OliverHi/RGBW-Controller/Pictures/RGBWController001.jpg

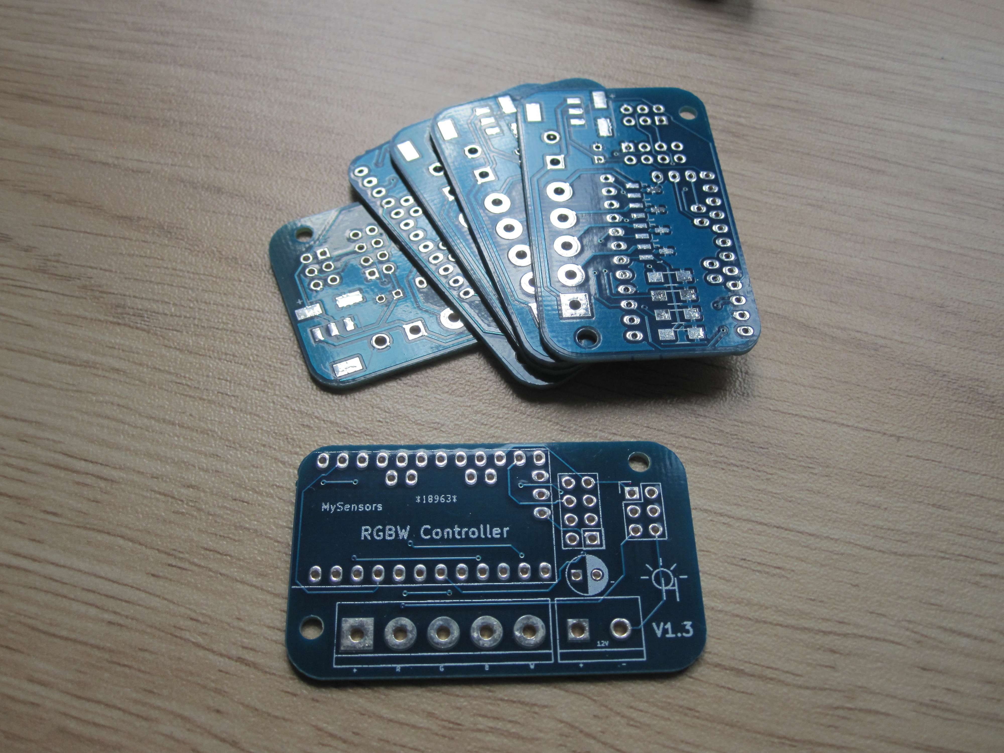
Pictures/RGBWController001.jpg
