OliverHi/RGBW-Controller/Pictures/RGBWController002.jpg

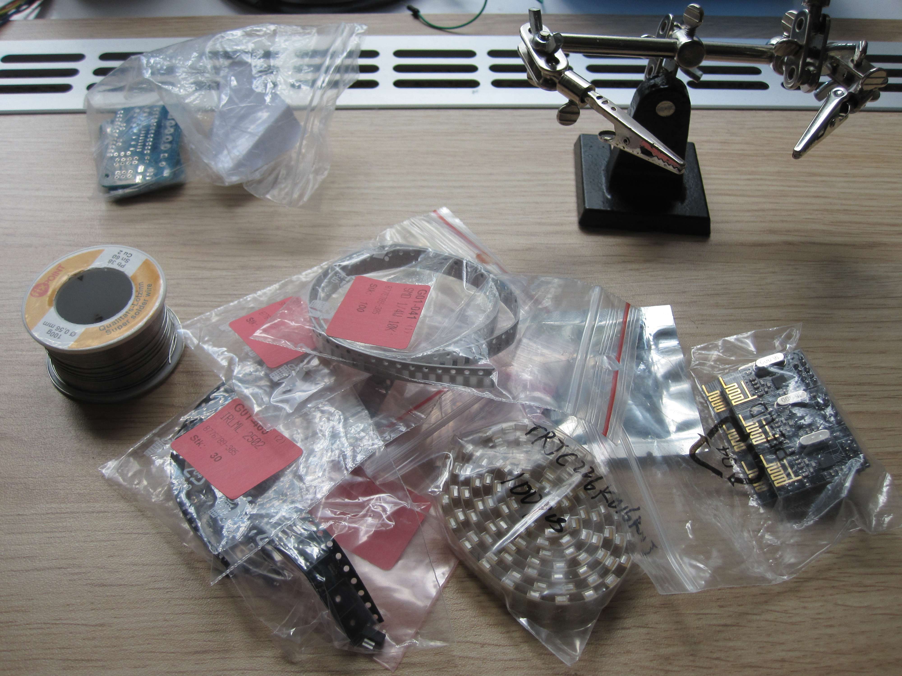
Pictures/RGBWController002.jpg
