OliverHi/RGBW-Controller/Pictures/RGBWController003.jpg

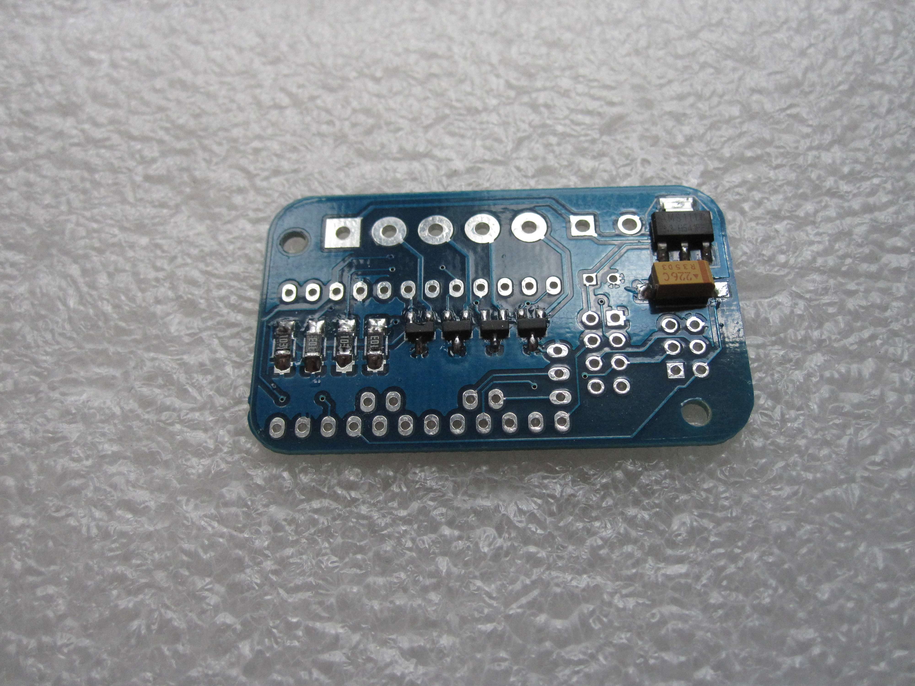
Pictures/RGBWController003.jpg
