OliverHi/RGBW-Controller/Pictures/RGBWController005.jpg

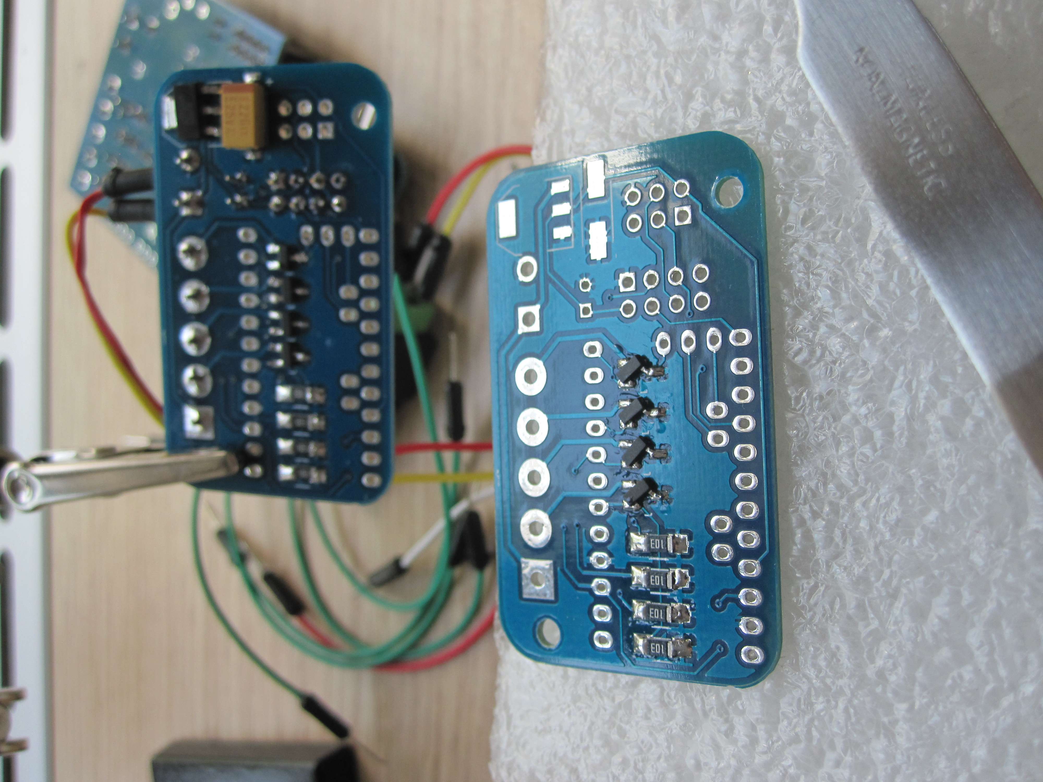
Pictures/RGBWController005.jpg
