OliverHi/RGBW-Controller/Pictures/RGBWController006.jpg

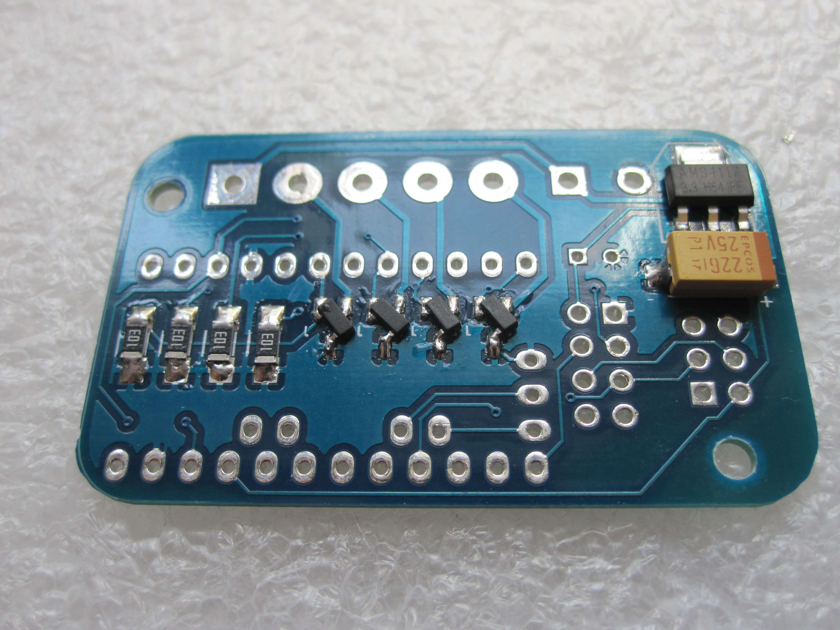
Pictures/RGBWController006.jpg
