OliverHi/RGBW-Controller/Pictures/RGBWController007.jpg

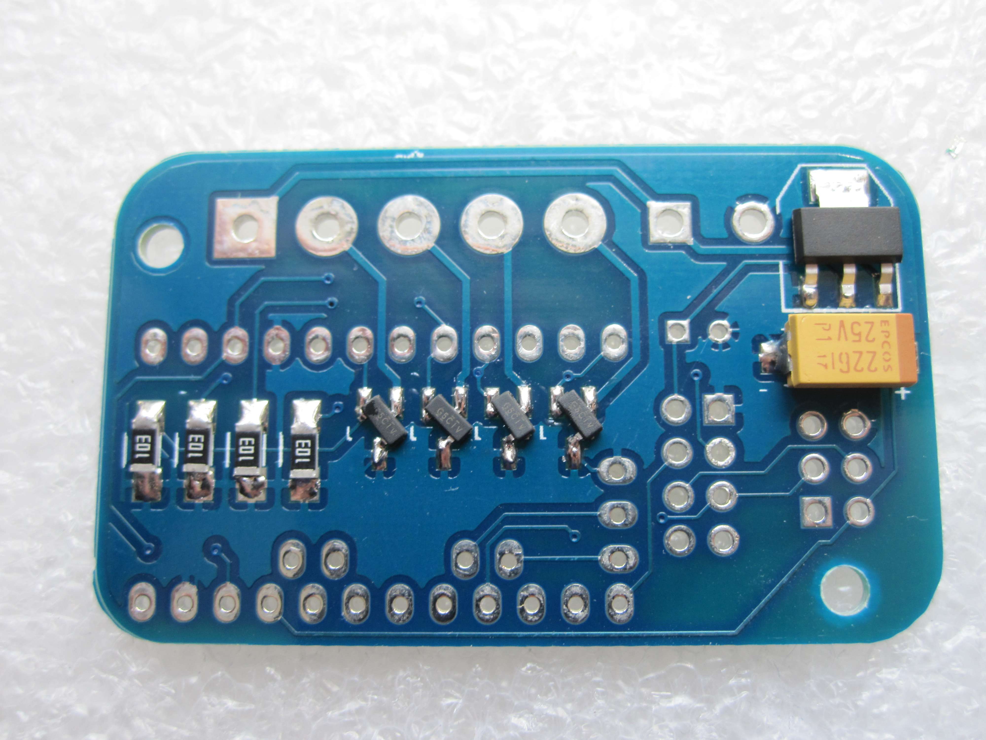
Pictures/RGBWController007.jpg
