OliverHi/RGBW-Controller/Pictures/RGBWController008.jpg

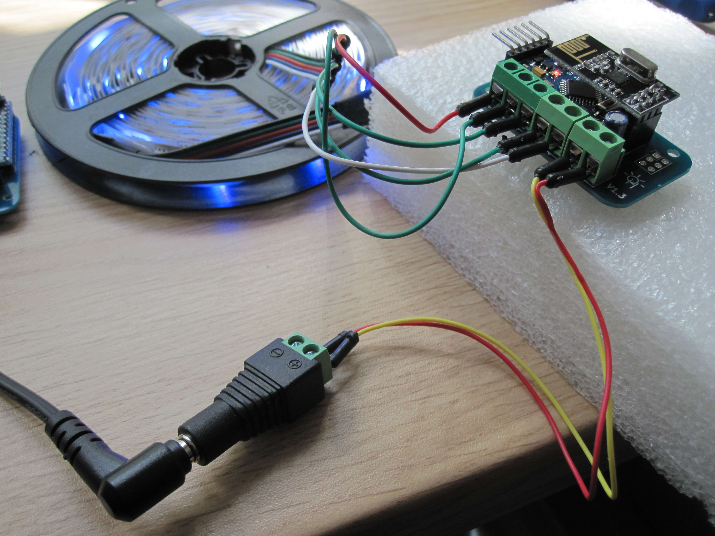
Pictures/RGBWController008.jpg
