OliverHi/RGBW-Controller/Pictures/RGBWController009.jpg

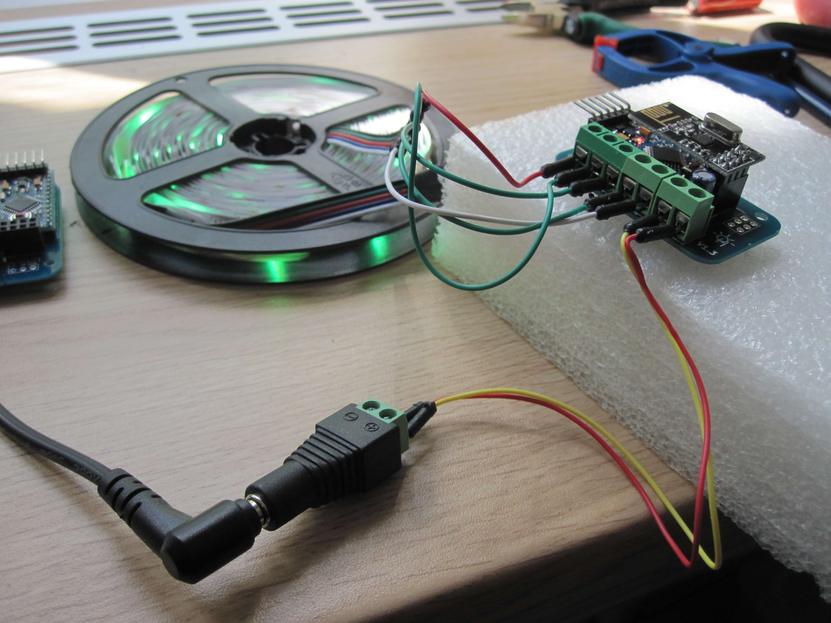
Pictures/RGBWController009.jpg
