OliverHi/RGBW-Controller/Pictures/RGBWController014.jpg

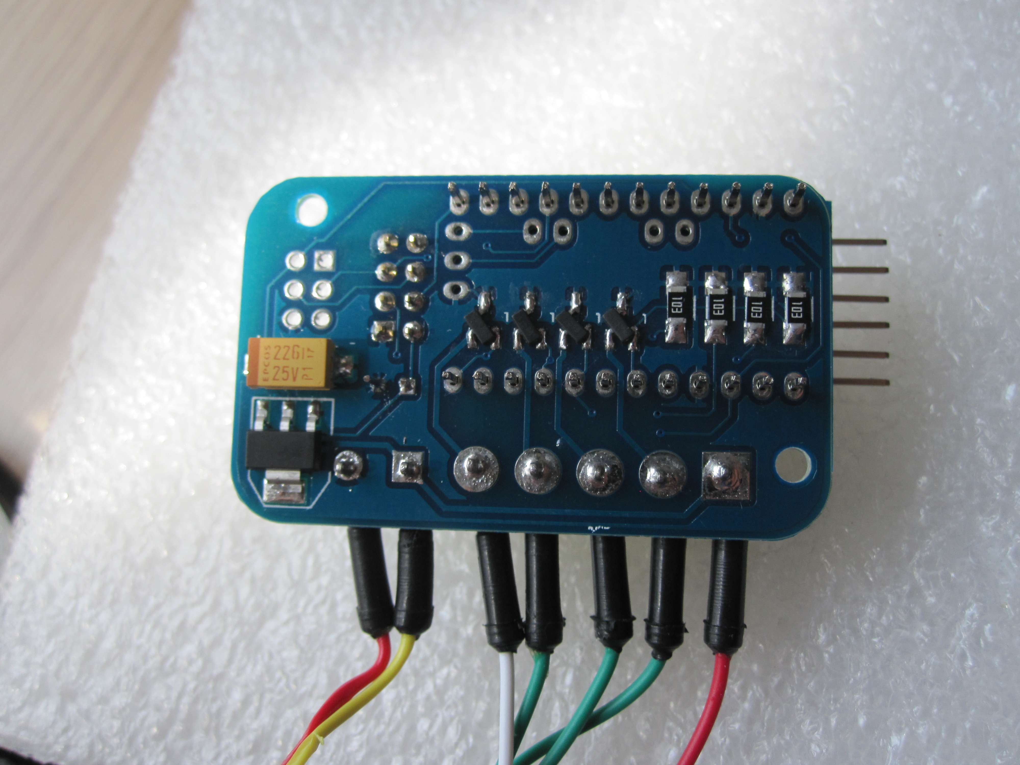
Pictures/RGBWController014.jpg
